FoR-Group1/OpenWhisker/calibration_platform/docs/figures/insert_ruler_into_mount.jpeg

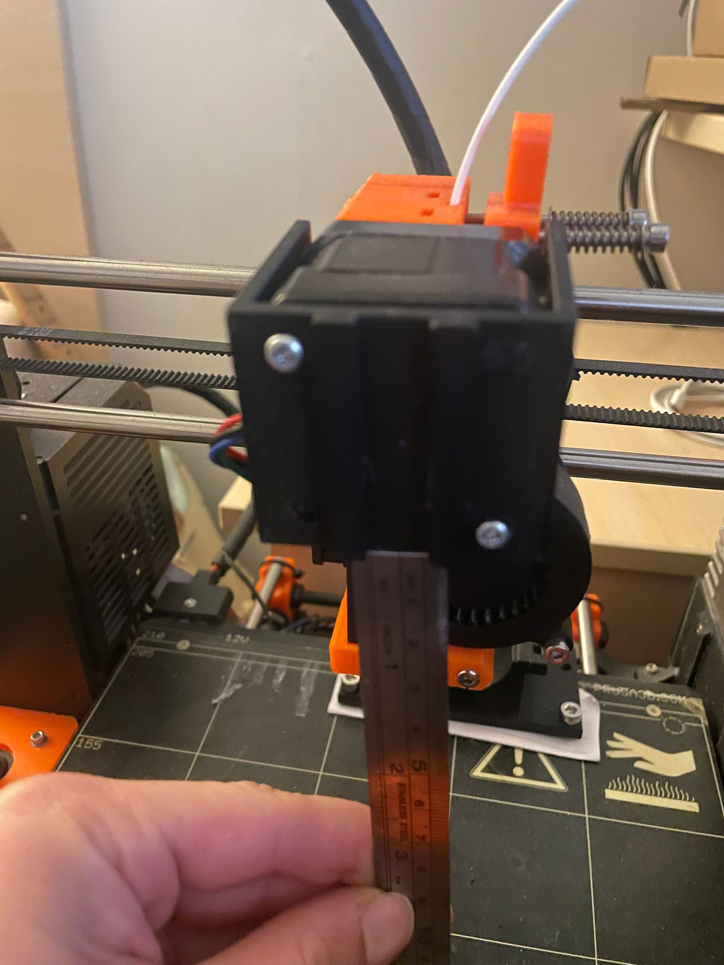
calibration_platform/docs/figures/insert_ruler_into_mount.jpeg
